FrozenSection/airbox/firmware/airbox/favicon_png.h

// favicon_png.h — "AB" monogram favicon (AirBox), served at /favicon.ico.
// GENERATED from ui/favicon.svg: dark tile #14222d, white AB, teal underline #4db6ac.
#ifndef FAVICON_PNG_H
#define FAVICON_PNG_H
const uint8_t FAVICON_PNG[] PROGMEM = {
  0x89,0x50,0x4e,0x47,0x0d,0x0a,0x1a,0x0a,0x00,0x00,0x00,0x0d,0x49,0x48,0x44,0x52,
  0x00,0x00,0x00,0x20,0x00,0x00,0x00,0x20,0x08,0x03,0x00,0x00,0x00,0x44,0xa4,0x8a,
  0xc6,0x00,0x00,0x00,0x60,0x50,0x4c,0x54,0x45,0x17,0x25,0x30,0xcf,0xd4,0xd8,0x36,
  0x69,0x6b,0xa0,0xa7,0xac,0x0c,0x21,0x2c,0x5a,0x64,0x6c,0x63,0x91,0x92,0x14,0x22,
  0x2d,0x51,0xc2,0xb6,0x13,0x22,0x2e,0x27,0x3a,0x43,0xb7,0xbe,0xc2,0xbc,0xc2,0xc6,
  0x38,0x81,0x7e,0x6e,0x78,0x80,0x14,0x22,0x2d,0x0d,0x19,0x25,0x00,0x00,0x00,0x0f,
  0x1b,0x2a,0x12,0x23,0x2a,0xf8,0xf9,0xfa,0x4f,0xbd,0xb2,0xe7,0xea,0xec,0x30,0x6c,
  0x6c,0x00,0x00,0x00,0x00,0x00,0x00,0x00,0x00,0x00,0x00,0x00,0x00,0x00,0x00,0x00,
  0x00,0x00,0x00,0x00,0x00,0x00,0x00,0x00,0x00,0x30,0x8c,0x29,0xd2,0x00,0x00,0x00,
  0x18,0x74,0x52,0x4e,0x53,0xf1,0xff,0xff,0xff,0x10,0xff,0xff,0x99,0xff,0x70,0xff,
  0xff,0xff,0xff,0xff,0xfc,0xff,0x00,0x11,0x2a,0xff,0xff,0xff,0xff,0xb2,0x75,0x40,
  0x97,0x00,0x00,0x01,0x15,0x49,0x44,0x41,0x54,0x78,0xda,0x95,0x93,0xeb,0x92,0x83,
  0x20,0x0c,0x85,0x4f,0x00,0xb1,0x6a,0xbb,0xa4,0x98,0xb2,0xef,0xff,0xa6,0x9b,0x28,
  0xed,0x28,0xb5,0xee,0xf4,0xfc,0x00,0x66,0xf2,0x91,0x0b,0x21,0xb8,0x2f,0x0a,0x21,
  0xbf,0x69,0xb5,0xc0,0xac,0x43,0x9f,0x0e,0x84,0x21,0xac,0x40,0x46,0xfa,0x20,0xcc,
  0x06,0x84,0x8f,0x76,0x25,0xb2,0x02,0x43,0x3a,0x51,0xaf,0x00,0xce,0x00,0x04,0xe4,
  0x74,0xaa,0xf9,0x1b,0x80,0x99,0xeb,0xc6,0xf5,0xb8,0x03,0x78,0x9c,0xc8,0x71,0x62,
  0xf8,0x2b,0x11,0xf9,0x8e,0x5b,0x00,0x51,0xc4,0x43,0x01,0x11,0xa2,0x22,0x52,0x89,
  0x4d,0x08,0x12,0x29,0xea,0x08,0x85,0x74,0xfd,0x31,0x78,0x07,0x70,0x27,0xde,0xdb,
  0x35,0x2c,0x58,0x94,0xd8,0x02,0x6a,0x75,0x72,0x65,0xf5,0xb0,0x84,0xb8,0x36,0x39,
  0x2c,0x9e,0x99,0xc4,0xad,0x00,0x95,0xd2,0xe4,0x80,0xce,0x72,0xb3,0x34,0x21,0x4a,
  0xb2,0x93,0x02,0xde,0x79,0x20,0xbb,0x47,0x1a,0x5f,0x01,0x06,0x52,0x91,0x71,0x0b,
  0xe8,0x0d,0xd2,0xc7,0xc1,0x24,0x5d,0x52,0x37,0xde,0x93,0x4c,0xbb,0x10,0x9a,0x62,
  0x64,0x2b,0xa5,0xf8,0x64,0x8f,0x20,0xc5,0xa3,0xc9,0xa1,0xf6,0x54,0x77,0x2c,0x67,
  0x6e,0xab,0xe0,0x67,0x3f,0xd2,0xb6,0x13,0x5f,0x75,0x93,0x1b,0xb5,0x00,0xe3,0x77,
  0xa7,0xf1,0xad,0x9b,0xf1,0xf2,0xd8,0xe8,0x12,0xd3,0xb3,0x8a,0x70,0x0c,0x3c,0x5e,
  0x65,0xd6,0x4f,0xcb,0xee,0xe6,0x36,0xba,0xb9,0x1a,0x22,0xbf,0xbe,0xfd,0x71,0x92,
  0xfd,0x3f,0x83,0x93,0x82,0x8d,0xde,0x09,0x31,0xaf,0xc3,0x9b,0xfb,0x43,0x04,0x7d,
  0x1d,0x5e,0x9b,0xef,0xf9,0x40,0xeb,0xfc,0xff,0x01,0xa5,0xa3,0x38,0xfe,0x90,0x46,
  0xfb,0xfc,0x00,0x00,0x00,0x00,0x49,0x45,0x4e,0x44,0xae,0x42,0x60,0x82,
};
const size_t FAVICON_PNG_LEN = sizeof(FAVICON_PNG);
#endif
