FrozenSection/airbox/firmware/airbox/web_ui.h

// web_ui.h — self-contained HTML/CSS/JS served from PROGMEM (flash).
// No external CDN: everything needed renders on a network with no internet.
// Two pages:
//   PORTAL_HTML — captive-portal WiFi provisioning (AP mode)
//   INDEX_HTML  — live dashboard / diagnostics / settings (STA mode)
//
// Charts are hand-drawn on <canvas>; no charting library. Keep this lean —
// it streams straight from flash via request->send_P(), costing ~0 heap.

#ifndef WEB_UI_H
#define WEB_UI_H

#include <pgmspace.h>

// =====================================================================
// Captive portal — WiFi provisioning
// =====================================================================
const char PORTAL_HTML[] PROGMEM = R"=====(<!DOCTYPE html>
<html lang="en"><head><meta charset="utf-8">
<meta name="viewport" content="width=device-width,initial-scale=1">
<title>AirBox — WiFi Setup</title>
<style>
:root{color-scheme:dark}
body{font-family:system-ui,-apple-system,Segoe UI,Roboto,sans-serif;background:#11151c;color:#e6edf3;margin:0;padding:18px;max-width:520px;margin:0 auto}
h1{font-size:1.3rem;margin:.2rem 0 1rem}
.card{background:#1b2230;border:1px solid #2a3446;border-radius:12px;padding:16px;margin-bottom:14px}
label{display:block;font-size:.85rem;color:#9fb0c3;margin:10px 0 4px}
select,input{width:100%;box-sizing:border-box;padding:10px;border-radius:8px;border:1px solid #33405a;background:#0e1320;color:#e6edf3;font-size:1rem}
button{width:100%;padding:12px;border:0;border-radius:9px;background:#2f6df6;color:#fff;font-size:1rem;font-weight:600;margin-top:14px;cursor:pointer}
button.alt{background:#33405a;margin-top:8px}
.row{display:flex;gap:8px;align-items:center}
.row input[type=checkbox]{width:auto}
small{color:#8493a8;display:block;margin-top:8px;line-height:1.4}
#msg{margin-top:10px;font-size:.95rem}
</style></head><body>
<h1>📡 AirBox — WiFi Setup</h1>
<div class="card">
  <label for="net">Your WiFi network</label>
  <select id="net"><option>Scanning…</option></select>
  <button class="alt" id="rescan" type="button">Rescan networks</button>
  <label for="pw">Password</label>
  <input id="pw" type="password" placeholder="network password" autocomplete="off">
  <div class="row" style="margin-top:8px"><input id="show" type="checkbox"><label for="show" style="margin:0">Show password</label></div>
  <button id="go" type="button">Connect</button>
  <div id="msg"></div>
  <small>The device will reboot and join your network. To change networks
  later, hold the BOOT button for 3 seconds, or use “Reconfigure WiFi” on the
  dashboard. Calibration data is preserved across a WiFi reset.</small>
</div>
<script>
var net=document.getElementById('net'),pw=document.getElementById('pw'),
    go=document.getElementById('go'),msg=document.getElementById('msg'),
    rescan=document.getElementById('rescan');
document.getElementById('show').onchange=function(e){pw.type=e.target.checked?'text':'password'};
// Escape untrusted text (SSIDs come from nearby APs — a maliciously named one
// must not be able to inject markup into this page, which holds the WiFi password).
function esc(s){return String(s).replace(/[&<>"]/g,function(c){return{'&':'&amp;','<':'&lt;','>':'&gt;','"':'&quot;'}[c];});}
function fill(list){
  if(!list.length){net.innerHTML='<option value="">No networks found</option>';return;}
  list.sort(function(a,b){return b.rssi-a.rssi});
  net.innerHTML=list.map(function(n){
    var lock=n.enc?'🔒':'';var bars=n.rssi>-60?'▂▄▆█':n.rssi>-72?'▂▄▆':'▂▄';
    return '<option value="'+esc(n.ssid)+'">'+esc(n.ssid)+' '+lock+' '+bars+'</option>';
  }).join('');
}
function load(){fetch('/scan').then(function(r){return r.json()}).then(function(d){
  if(d.scanning){setTimeout(load,1200);net.innerHTML='<option>Scanning…</option>';return;}
  fill(d.networks||[]);
}).catch(function(){setTimeout(load,1500)});}
rescan.onclick=function(){net.innerHTML='<option>Scanning…</option>';fetch('/rescan').then(load)};
go.onclick=function(){
  var ssid=net.value;if(!ssid){msg.textContent='Pick a network first.';return;}
  go.disabled=true;msg.textContent='Saving…';
  fetch('/save',{method:'POST',headers:{'Content-Type':'application/x-www-form-urlencoded'},
    body:'ssid='+encodeURIComponent(ssid)+'&pass='+encodeURIComponent(pw.value)})
  .then(function(){msg.innerHTML='✅ Saved. The device is rebooting and joining <b>'+esc(ssid)+'</b>.<br>This page will stop responding — reconnect to your normal WiFi.';})
  .catch(function(){msg.textContent='Saved (device rebooting).';});
};
load();
</script></body></html>)=====";

// =====================================================================
// Dashboard / Diagnostics / Settings
// =====================================================================
// >>> GENERATED BY ui/build-web-ui.py — DO NOT EDIT BELOW >>>
const uint8_t INDEX_HTML_GZ[] PROGMEM = {
  0x1f,0x8b,0x08,0x00,0x00,0x00,0x00,0x00,0x02,0xff,0xcd,0xbd,0xc9,0x72,0xe3,0xc8,
  0xb2,0x28,0xb8,0xcf,0xaf,0x88,0xe4,0xb9,0x59,0x00,0x8b,0xe0,0x3c,0x88,0x22,0x45,
  0x65,0x6b,0x4c,0x29,0x35,0xa6,0x28,0xe5,0x58,0x69,0x69,0x20,0x00,0x12,0x90,0x40,
  0x80,0x02,0x40,0x91,0x94,0x52,0x6d,0x65,0x6f,0x71,0xed,0xad,0xef,0x7d,0x9b,0xfb,
  0xec,0xb5,0x59,0xaf,0xda,0xac,0x77,0xc7,0xac,0x17,0x77,0x5f,0x9f,0x52,0x5f,0xd2,
  0xee,0x1e,0x81,0x89,0x83,0x94,0x79,0xce,0xb9,0xc7,0x5e,0x56,0x89,0x24,0x80,0x08,
  0x8f,0x08,0x0f,0x0f,0x9f,0xc2,0xc3,0xb1,0xf1,0x72,0xf7,0x6c,0xe7,0xf2,0xd3,0xf9,
  0x1e,0x33,0x83,0xa1,0xbd,0xf9,0x62,0xe3,0x65,0x3e,0xff,0x82,0xb1,0x2d,0xcb,0xdb,
  0x76,0xa7,0xec,0xcf,0xdf,0xff,0x07,0xf3,0x0d,0xbb,0x9f,0xd7,0x5c,0x27,0x50,0x2d,
  0xc7,0xd0,0x99,0xae,0xfa,0x66,0xcf,0x55,0x3d,0x9d,0xf5,0x5d,0x8f,0x4d,0x8c,0xde,
  0xb7,0xb1,0x55,0x30,0x99,0x7c,0x78,0xba,0xbb,0xf7,0xf1,0xdb,0xc1,0xe5,0xc9,0x71,
  0xb6,0x00,0x00,0x4e,0x5d,0x66,0x4c,0x03,0xc3,0x73,0x54,0x9b,0xed,0xec,0x9e,0xb2,
  0x22,0x14,0x77,0x02,0x1f,0xbe,0x6d,0xab,0xe7,0xa9,0x9e,0x65,0xf8,0x05,0xf6,0x5e,
  0x75,0x2c,0xdb,0x56,0xd9,0xdb,0x6e,0x81,0xed,0xa8,0xce,0x9d,0xea,0x33,0xcd,0x54,
  0xbd,0xc0,0x47,0x08,0xe7,0xae,0x6d,0x43,0x79,0x75,0x64,0x15,0x75,0x35,0x50,0x99,
  0x5c,0xf3,0xb3,0x2c,0xc7,0x6f,0x98,0x96,0x1f,0xb8,0xde,0x8c,0xc9,0x8d,0x92,0x9f,
  0x6d,0xb3,0x91,0xeb,0x07,0xa2,0xa8,0x6f,0x04,0x81,0xe5,0x0c,0x38,0x04,0xcf,0xb8,
  0xb3,0x8c,0x89,0xcf,0xfc,0x40,0x75,0x74,0xd5,0x76,0x1d,0x83,0xdd,0x59,0x2a,0x53,
  0xd9,0xd0,0xd5,0x6e,0xf2,0x04,0xb5,0xaf,0xda,0x76,0x4f,0xd5,0x6e,0xd8,0xc4,0x34,
  0x1c,0x16,0x98,0x06,0xdb,0x3a,0x3f,0x64,0x96,0xcf,0xd4,0x9e,0x6f,0x38,0x41,0xe1,
  0x45,0x3e,0x0f,0x48,0x41,0xdc,0x30,0x5b,0x75,0x06,0x9d,0x8c,0xe1,0x64,0xf0,0x86,
  0xa1,0xea,0xf0,0x35,0x34,0x00,0x04,0x76,0x19,0x9a,0xed,0x64,0xc6,0x41,0x3f,0xdf,
  0xcc,0x14,0xc3,0xfb,0x8e,0x3a,0x34,0x3a,0x19,0xec,0xc1,0xc8,0xf5,0x82,0x0c,0x43,
  0x1c,0x02,0xc8,0x4e,0x66,0x62,0xe9,0x81,0xd9,0xd1,0xa1,0x73,0x9a,0x91,0xa7,0x0b,
  0xc5,0x72,0xac,0xc0,0x52,0xed,0xbc,0xaf,0xa9,0xb6,0xd1,0x29,0x13,0x10,0xdb,0x72,
  0x6e,0x98,0x67,0xd8,0x9d,0x8c,0x05,0x55,0x33,0x2c,0x98,0x8d,0x00,0x9e,0x35,0x54,
  0x07,0x46,0x71,0xe4,0x0c,0x32,0xcc,0xf4,0x8c,0x7e,0x27,0x53,0xec,0xab,0x77,0x58,
  0xa0,0x00,0x1f,0x54,0x2f,0xb0,0x02,0xdb,0xd8,0xe4,0x33,0xb8,0x51,0xe4,0x57,0x2f,
  0x36,0xfc,0x60,0x86,0xdf,0x2d,0xcf,0x75,0x83,0x07,0x40,0x8e,0xe6,0xda,0xae,0x07,
  0xed,0x99,0xc6,0xd0,0x68,0xe9,0xaa,0x77,0xd3,0x86,0x9b,0xf9,0x7c,0x6f,0xd0,0x72,
  0x6f,0x6c,0xcd,0x94,0x4b,0x85,0x72,0xb3,0xce,0x4a,0x85,0x52,0xb9,0xc2,0xd6,0x4a,
  0x80,0xe4,0x7c,0x1e,0xfa,0xd3,0xfa,0x4b,0xbf,0x66,0xf4,0x8d,0x26,0x2f,0xac,0x5b,
  0xc3,0x96,0x37,0xe8,0xa9,0x72,0xa5,0x56,0x53,0x2a,0xd5,0x75,0xf8,0xab,0x28,0xa5,
  0x42,0x9d,0x4a,0xf7,0x81,0x5e,0x82,0x65,0x8f,0xab,0xcd,0x2c,0xaf,0xae,0x01,0x15,
  0x89,0x02,0xf5,0xba,0x12,0xfe,0x41,0x93,0x15,0x0e,0x01,0x9f,0x57,0x96,0x16,0xa8,
  0x09,0x08,0x80,0x22,0x63,0x69,0x81,0x35,0x02,0x80,0x8f,0x97,0x02,0x28,0x8b,0xfa,
  0x41,0x34,0xd8,0xb5,0x0a,0x8c,0xb5,0x5c,0x65,0xd8,0x39,0x78,0x60,0xc6,0x0f,0x4a,
  0xf8,0xa0,0xcc,0x2a,0xb5,0x2a,0x3d,0x19,0x45,0x4f,0x1a,0x4d,0x7c,0x52,0x61,0xd5,
  0x92,0x40,0xcf,0x1c,0xb0,0x0a,0x2b,0xd7,0x4b,0xa2,0xa1,0x81,0xeb,0xea,0xf1,0x63,
  0xaa,0x58,0x62,0xe5,0x46,0x33,0xc4,0x94,0x17,0x3d,0x6c,0x56,0x79,0x7b,0xcd,0x0a,
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
};
const size_t INDEX_HTML_GZ_LEN = sizeof(INDEX_HTML_GZ);
// <<< END GENERATED <<<

#endif // WEB_UI_H
